PiSugar/PiSugar/model/pisugar_comp.JPG

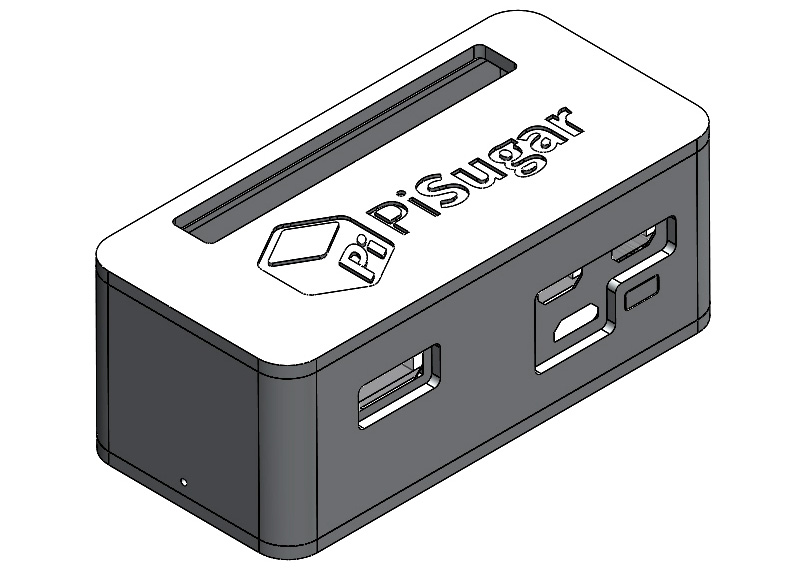
model/pisugar_comp.JPG
