PiSugar/PiSugar/model/pisugar_nobatt_shell.JPG

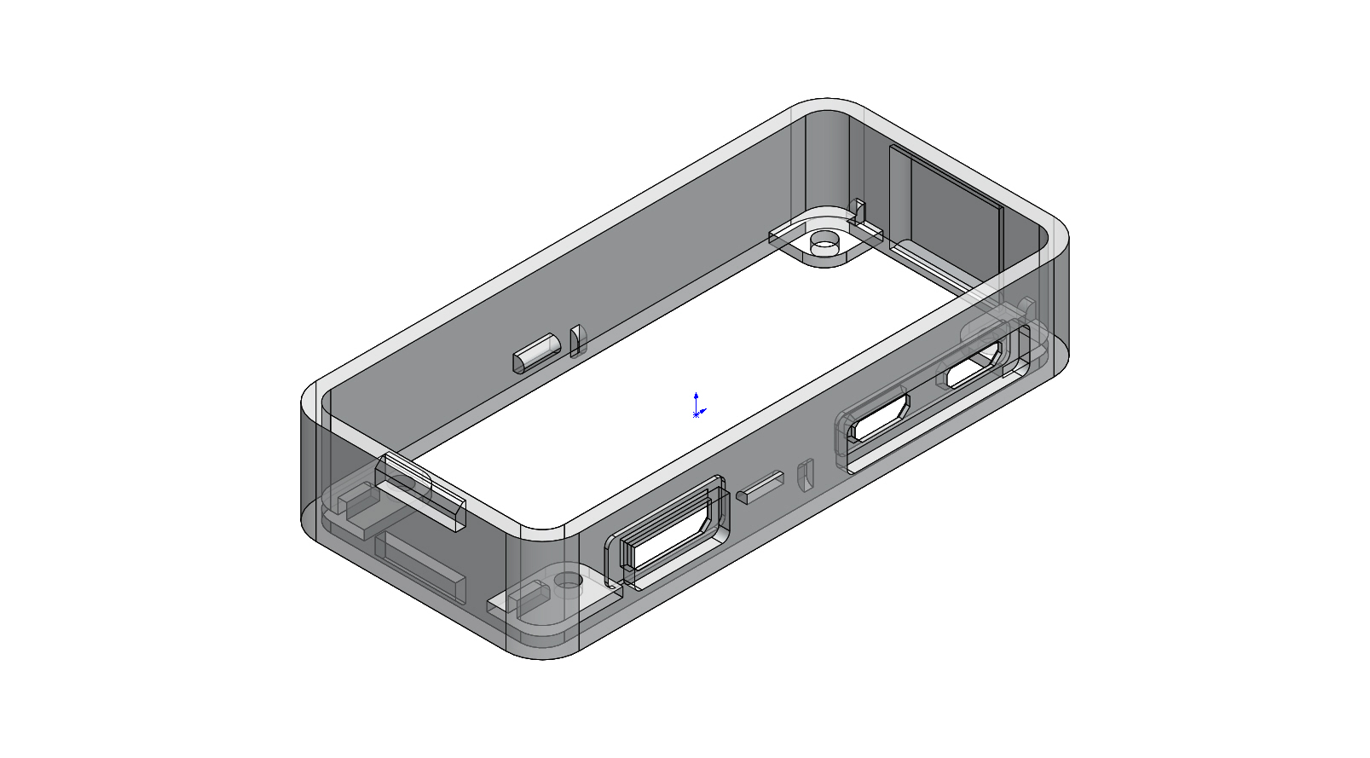
model/pisugar_nobatt_shell.JPG
