PiSugar/PiSugar/model_pro/comp-1.JPG

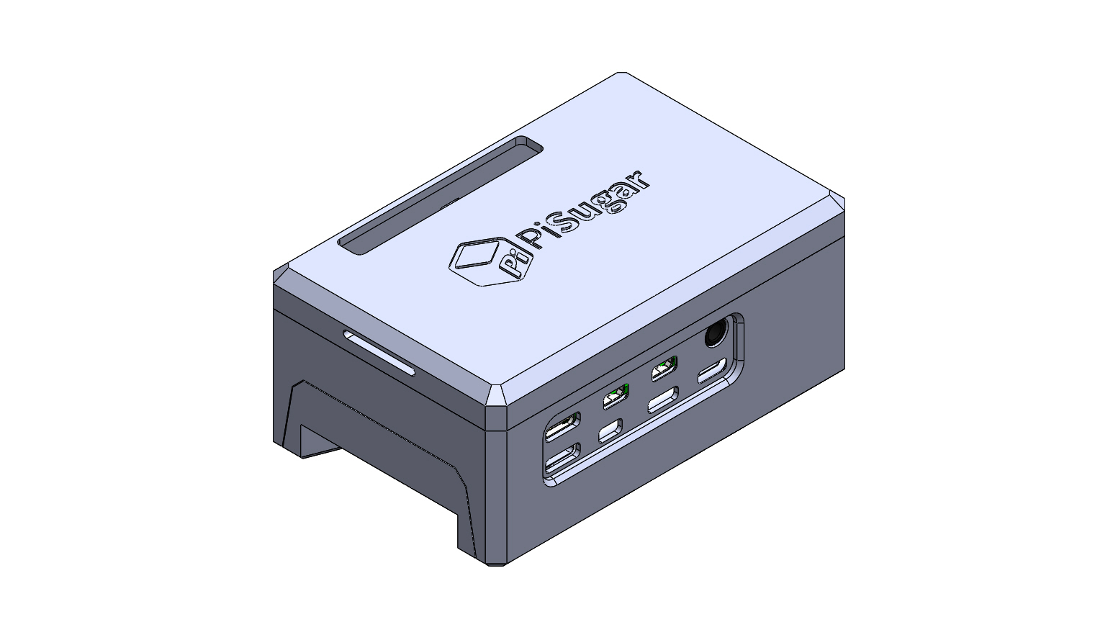
model_pro/comp-1.JPG
