PiSugar/PiSugar/model_pro/comp-2.JPG

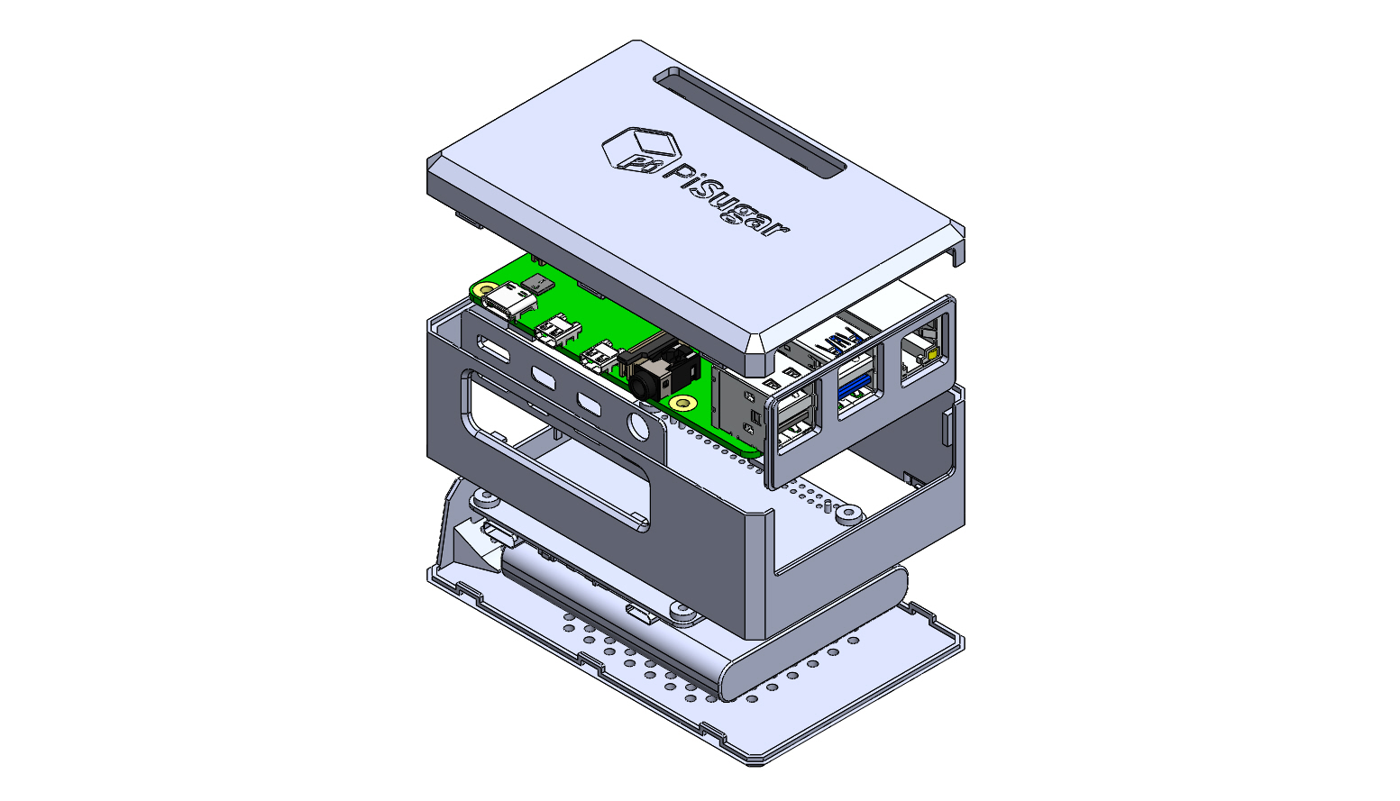
model_pro/comp-2.JPG
