PiSugar/PiSugar/model3/step/pisugar_case_common_cap.STEP

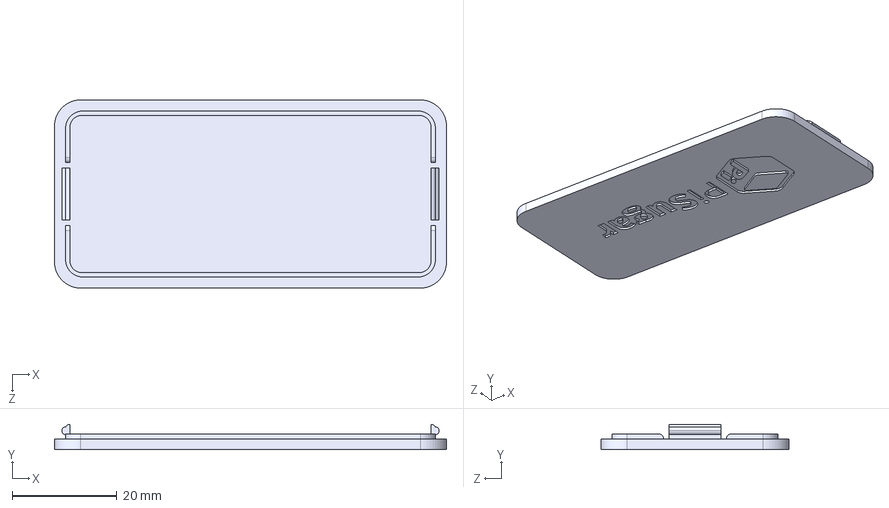
[picture p33: CAD file, 2024-06-06]
model3/step/pisugar_case_common_cap.STEP
75.0 x 4.80 x 36.0 mm
