PiSugar/PiSugar/model_pro/lid/3.52inch-epaper/3.52inch-epaper.SLDPRT

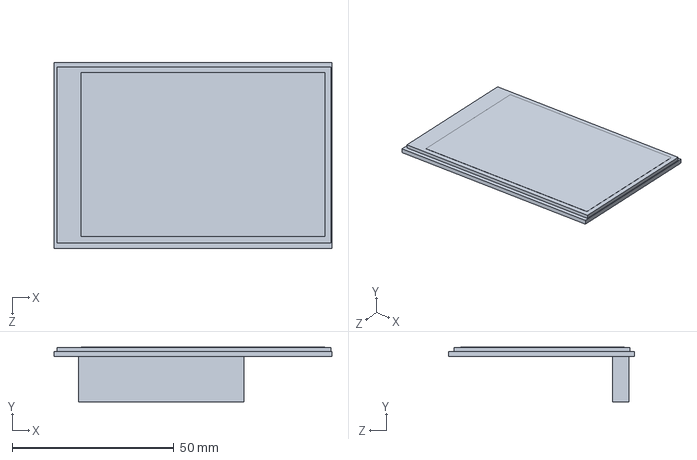
[picture p34: CAD file, 2024-07-05]
model_pro/lid/3.52inch-epaper/3.52inch-epaper.SLDPRT
86.0 x 17.0 x 57.4 mm
