PiSugar/PiSugar/model_pro/pisugar3plus.STEP

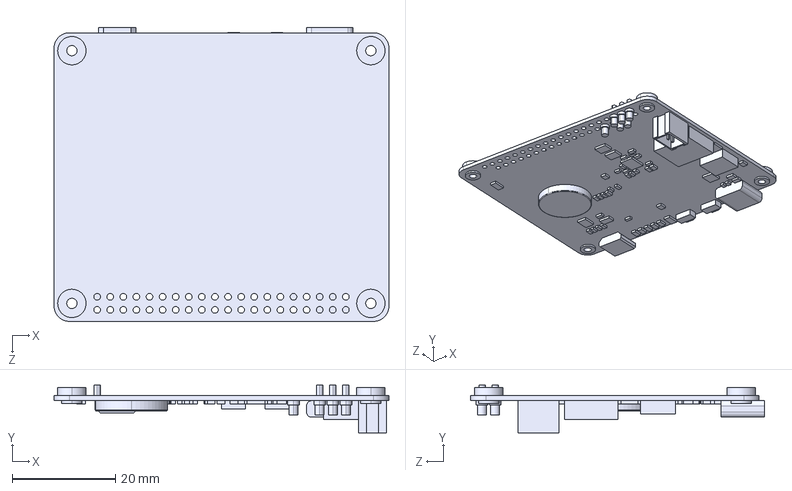
[picture p35: CAD file, 2025-03-03]
model_pro/pisugar3plus.STEP
65.0 x 9.22 x 57.0 mm
