PiSugar/PiSugar/model_pro/step/switch.STEP

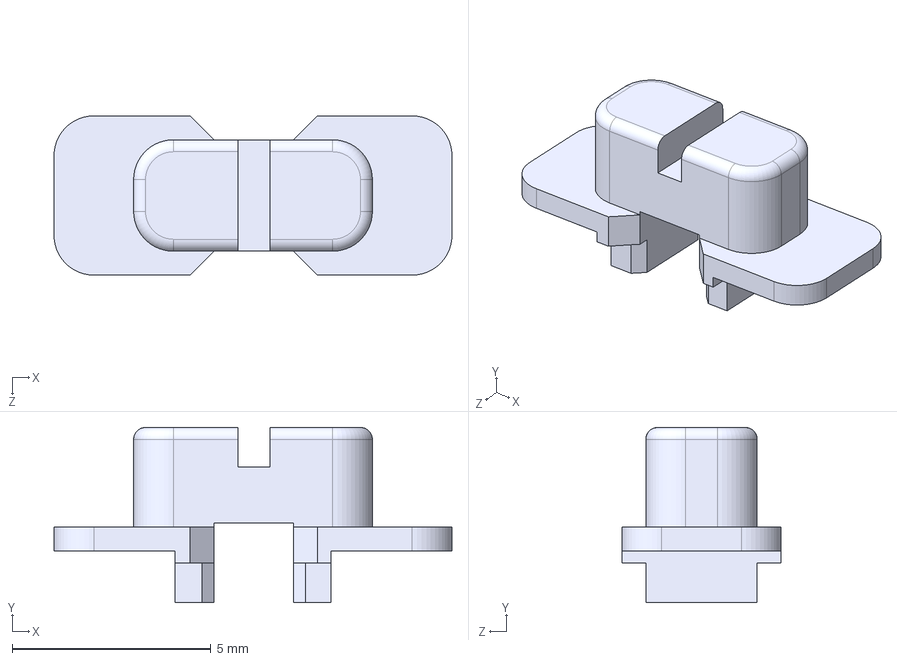
[picture p36: CAD file, 2024-06-06]
model_pro/step/switch.STEP
10.0 x 4.40 x 4.00 mm
