PiSugar/PiSugar/model/pisugar_case_shell_xl.SLDPRT

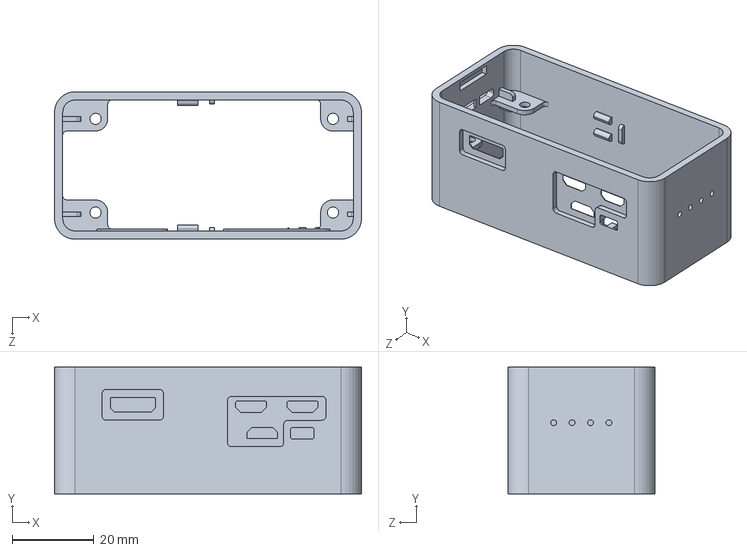
[picture p37: CAD file, 2019-11-30]
model/pisugar_case_shell_xl.SLDPRT
75.0 x 31.0 x 36.0 mm
