PiSugar/PiSugar/model2/pisugar2_button_batch.SLDPRT

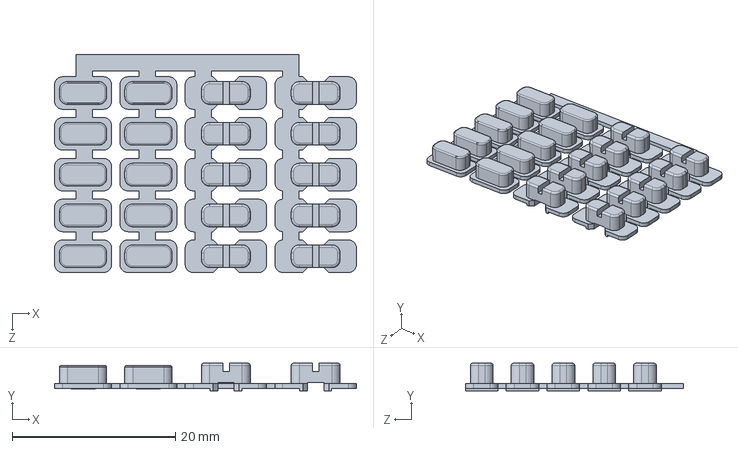
[picture p38: CAD file, 2022-10-15]
model2/pisugar2_button_batch.SLDPRT
37.0 x 3.40 x 26.7 mm
