PiSugar/PiSugar/model3/step/pisugar3_button.STEP

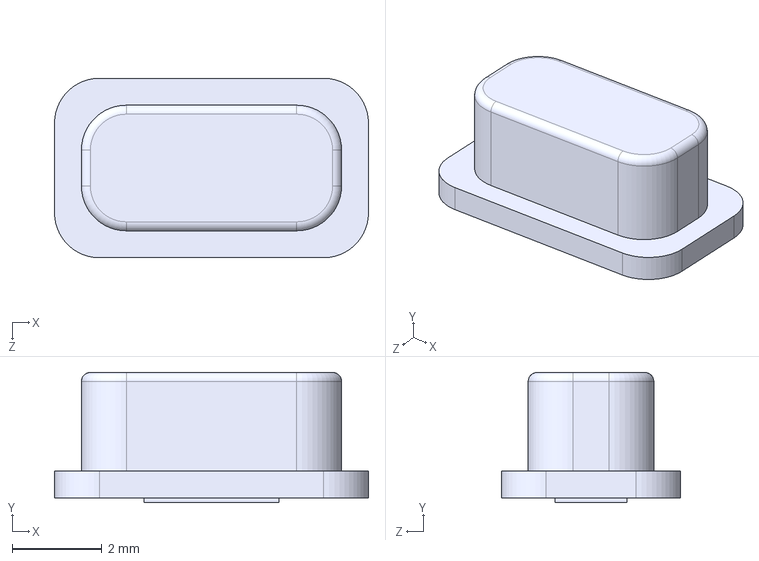
[picture p39: CAD file, 2024-06-06]
model3/step/pisugar3_button.STEP
7.00 x 2.90 x 4.00 mm
