PiSugar/PiSugar/model_pro/step/port-panel-3b-2p.STEP

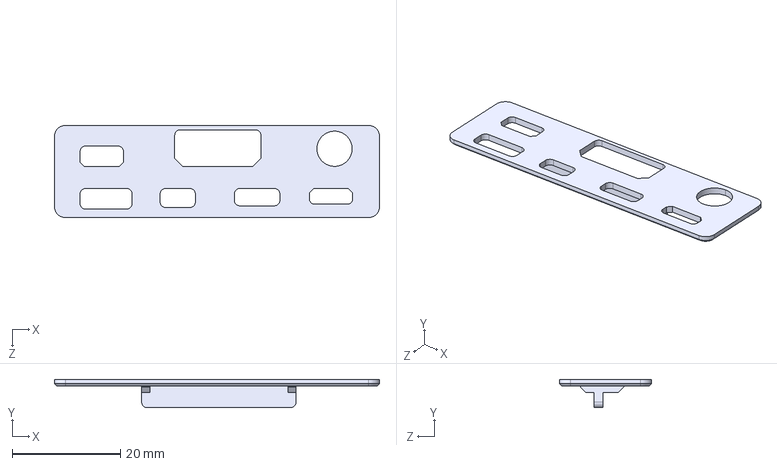
[picture p40: CAD file, 2024-06-06]
model_pro/step/port-panel-3b-2p.STEP
60.0 x 5.20 x 17.0 mm
