PiSugar/PiSugar/model_pro/top.SLDPRT

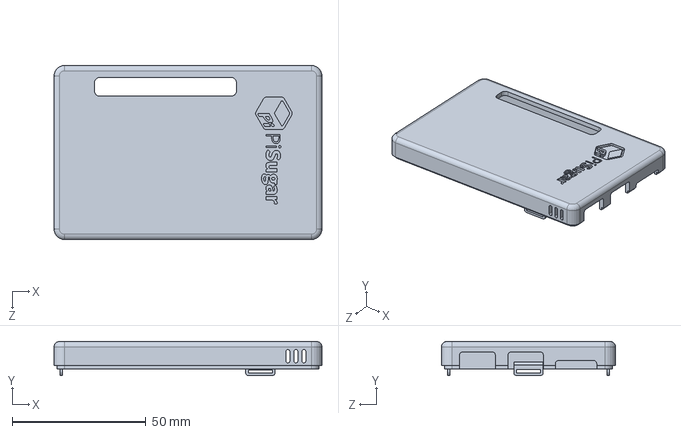
[picture p41: CAD file, 2024-06-06]
model_pro/top.SLDPRT
100.0 x 12.7 x 65.0 mm
