PiSugar/PiSugar/model2/pisugar2_shell_thin.SLDPRT

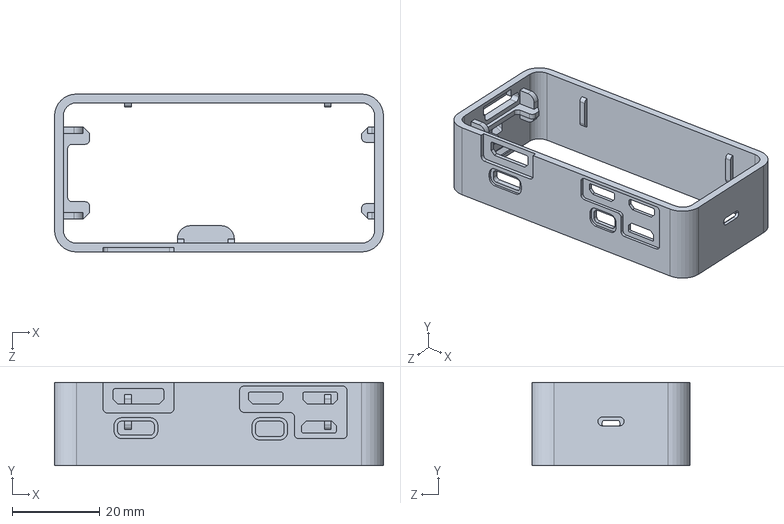
[picture p42: CAD file, 2021-06-01]
model2/pisugar2_shell_thin.SLDPRT
75.0 x 19.0 x 36.0 mm
