PiSugar/PiSugar/model3/step/pisugar3_shell_xl.STEP

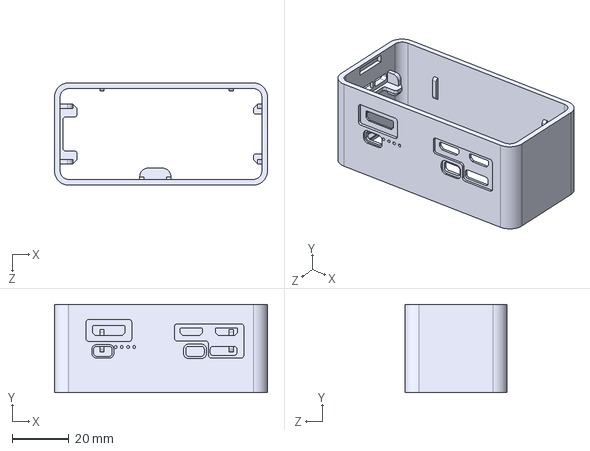
[picture p43: CAD file, 2024-06-06]
model3/step/pisugar3_shell_xl.STEP
75.0 x 31.0 x 36.0 mm
