PiSugar/PiSugar/model_pro/Ras Pi 3B+.SLDPRT

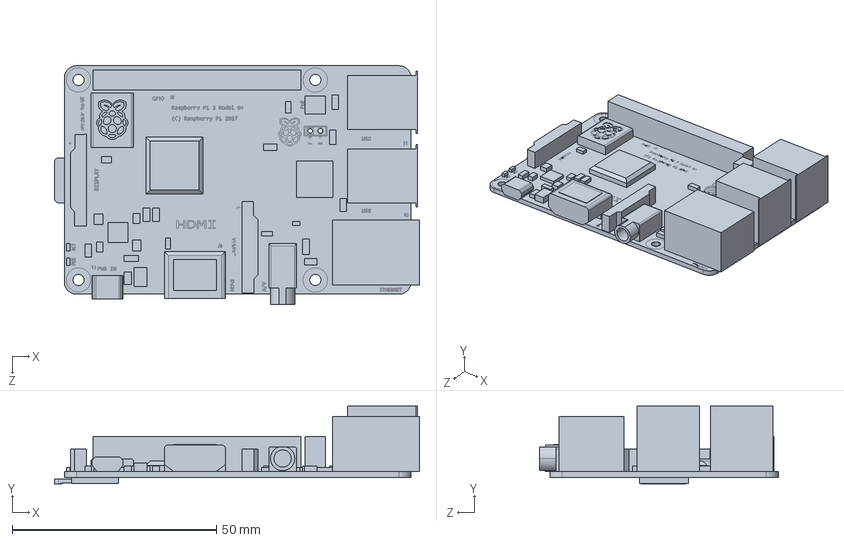
[picture p44: CAD file, 2024-06-06]
model_pro/Ras Pi 3B+.SLDPRT
89.4 x 19.1 x 58.5 mm
