PiSugar/PiSugar/model/pisugar_case_thin_shell.SLDPRT

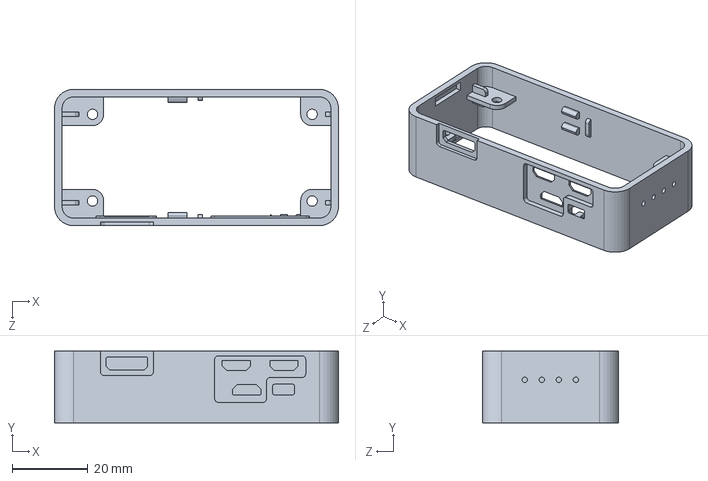
[picture p45: CAD file, 2019-11-04]
model/pisugar_case_thin_shell.SLDPRT
75.0 x 19.0 x 36.0 mm
