PiSugar/PiSugar/model_pro/bottom.SLDPRT

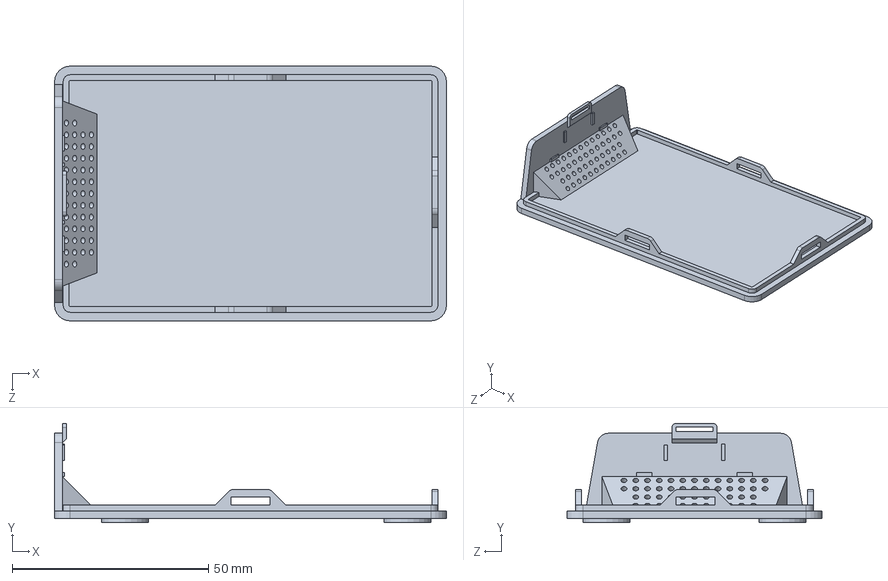
[picture p46: CAD file, 2024-06-06]
model_pro/bottom.SLDPRT
100.0 x 25.3 x 65.0 mm
