PiSugar/PiSugar/model_pro/step/pro_shell.STEP

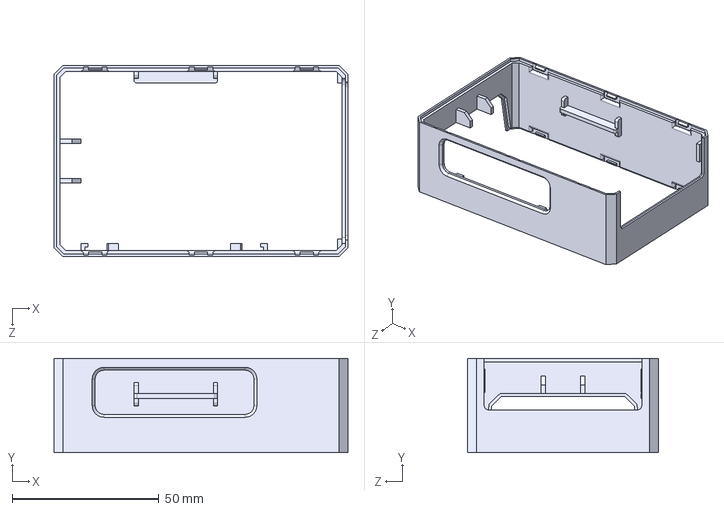
[picture p47: CAD file, 2024-06-06]
model_pro/step/pro_shell.STEP
100.0 x 32.0 x 65.0 mm
