PiSugar/PiSugar/model/pisugar_thin_nobatt_shell.SLDPRT

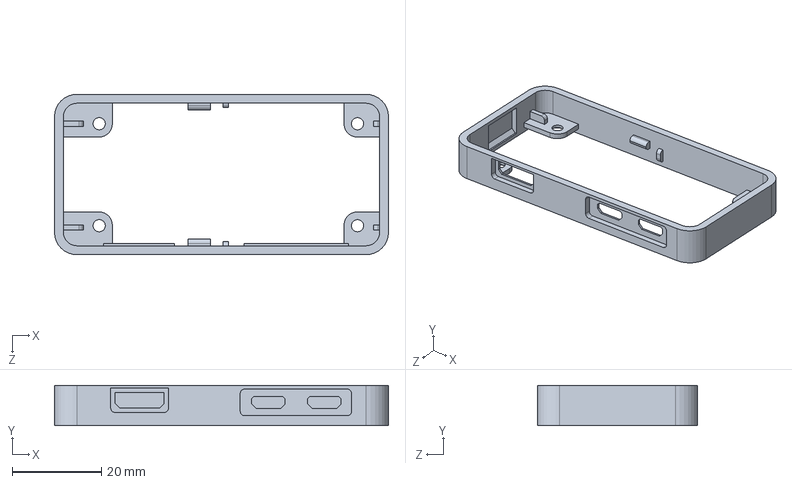
[picture p48: CAD file, 2019-06-25]
model/pisugar_thin_nobatt_shell.SLDPRT
75.0 x 9.00 x 36.0 mm
