PiSugar/PiSugar/model_pro/fan.SLDPRT

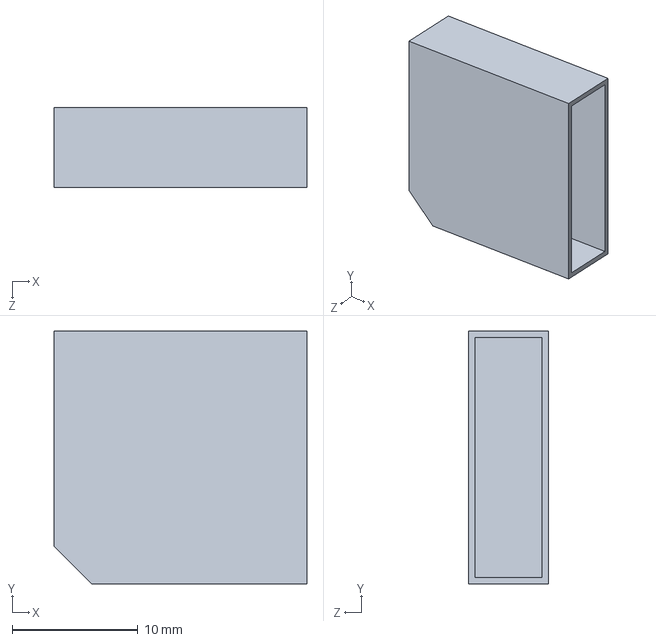
[picture p49: CAD file, 2024-06-06]
model_pro/fan.SLDPRT
20.2 x 20.2 x 6.36 mm
