PiSugar/PiSugar/model/pisugar_nobatt_shell.SLDPRT

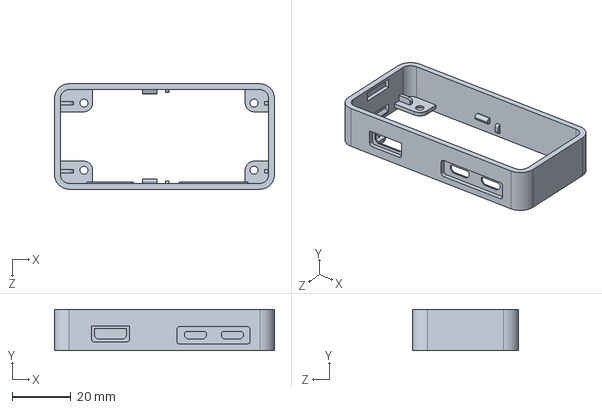
[picture p51: CAD file, 2019-06-25]
model/pisugar_nobatt_shell.SLDPRT
75.0 x 14.0 x 36.0 mm
