PiSugar/PiSugar/model2/pisugar2_switch.SLDPRT

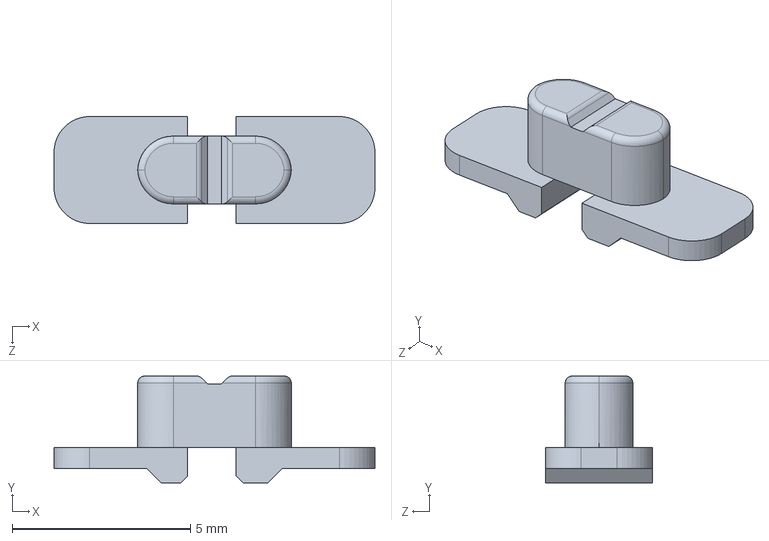
[picture p52: CAD file, 2020-06-27]
model2/pisugar2_switch.SLDPRT
9.00 x 3.00 x 3.00 mm
