PiSugar/PiSugar/model_pro/batt5000.SLDPRT

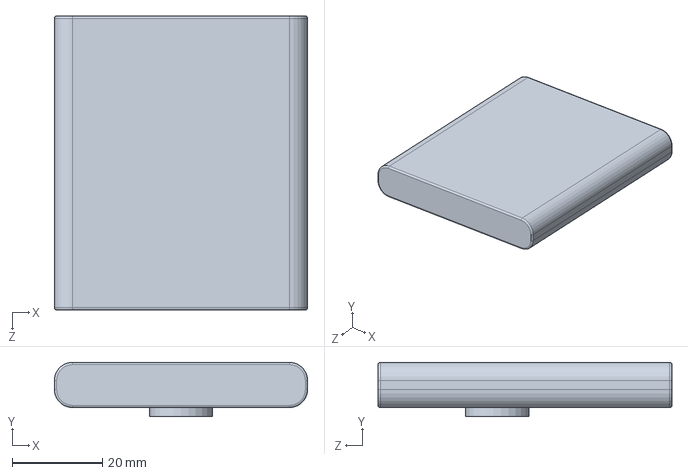
[picture p53: CAD file, 2024-06-06]
model_pro/batt5000.SLDPRT
56.0 x 12.0 x 65.0 mm
