PiSugar/PiSugar/model/pisugar_holder.SLDPRT

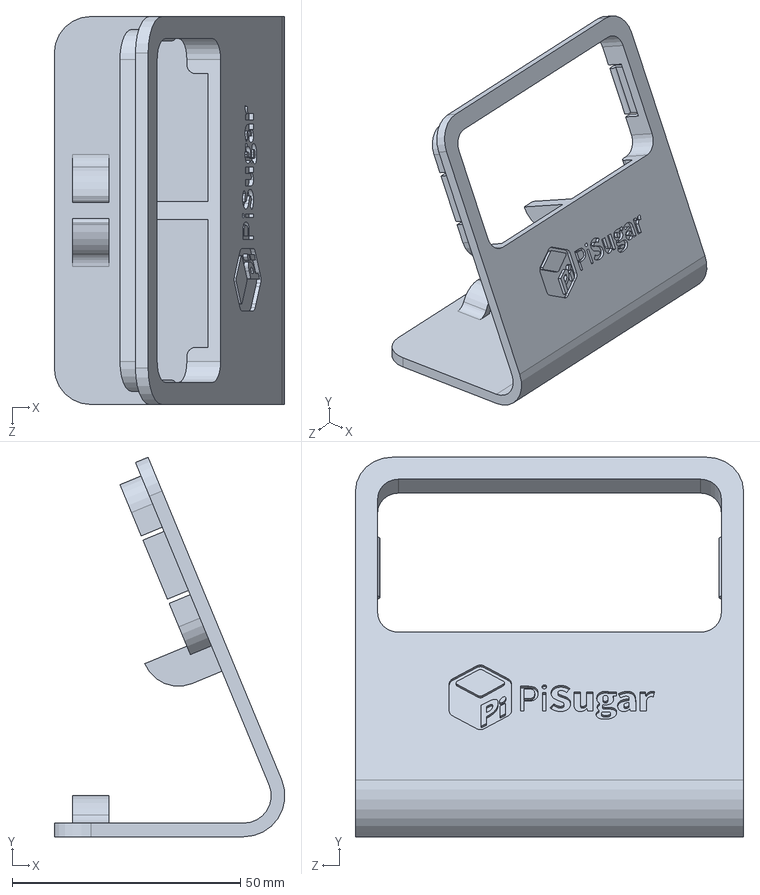
[picture p54: CAD file, 2019-05-16]
model/pisugar_holder.SLDPRT
50.5 x 83.1 x 85.0 mm
