PiSugar/PiSugar/model2/pisugar2_shell_xl - pisugar2_switch-1.STL

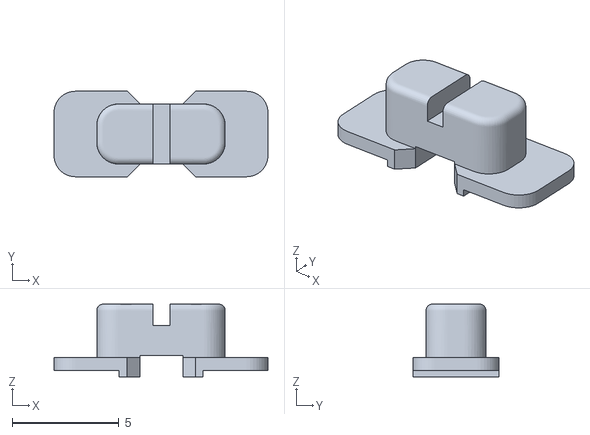
[picture p55: CAD file, 2020-06-27]
model2/pisugar2_shell_xl - pisugar2_switch-1.STL
10.0 x 4.00 x 3.40
