PiSugar/PiSugar/model/glass.SLDPRT

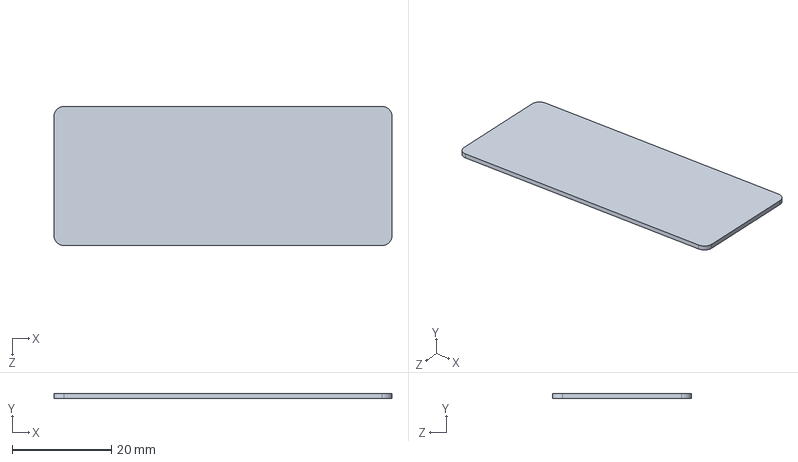
[picture p56: CAD file, 2019-04-10]
model/glass.SLDPRT
68.0 x 1.00 x 28.0 mm
