PiSugar/PiSugar/model/pisugar_case_button_comp.SLDPRT

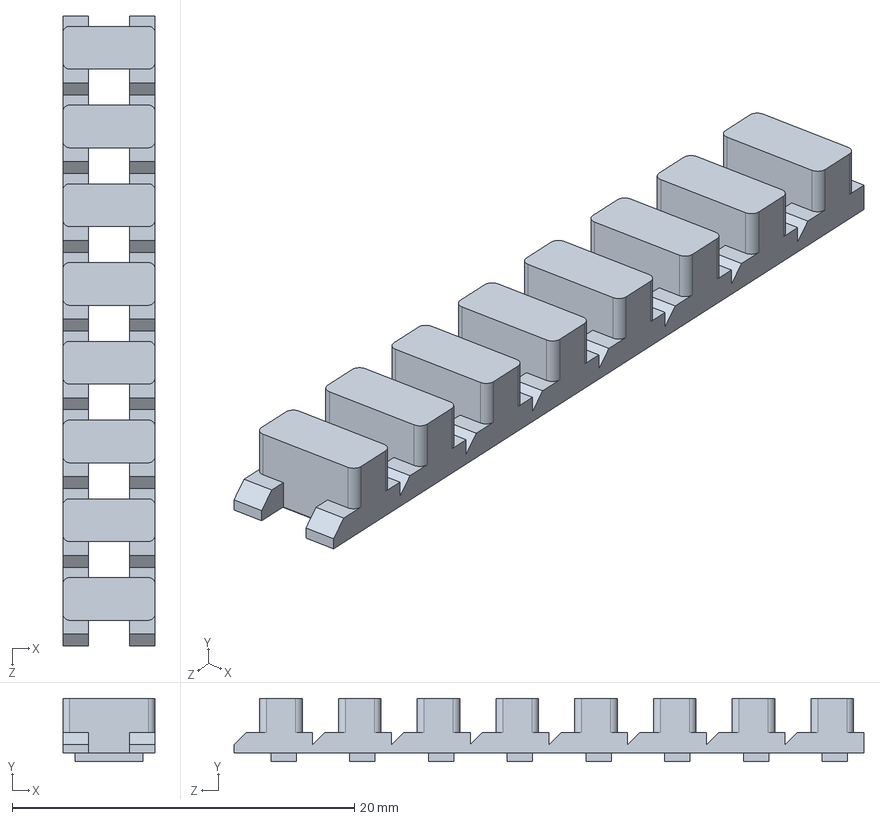
[picture p57: CAD file, 2019-04-10]
model/pisugar_case_button_comp.SLDPRT
5.40 x 3.70 x 36.8 mm
