PiSugar/PiSugar/model/pisugar_case_button.SLDPRT

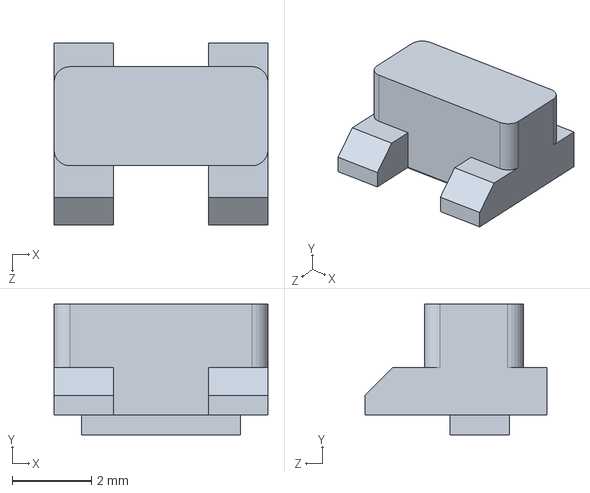
[picture p58: CAD file, 2019-04-10]
model/pisugar_case_button.SLDPRT
5.40 x 3.30 x 4.60 mm
