PiSugar/PiSugar/model_pro/pro - usb-panel-3b-1.STL

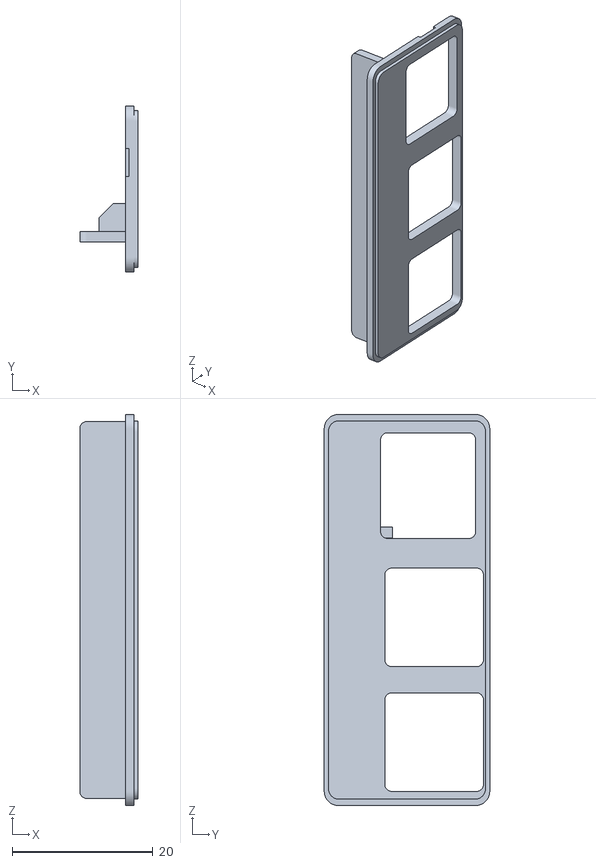
[picture p59: CAD file, 2022-04-29]
model_pro/pro - usb-panel-3b-1.STL
8.30 x 23.5 x 55.5
