PiSugar/PiSugar/model/pisugar_case_top_cap.SLDPRT

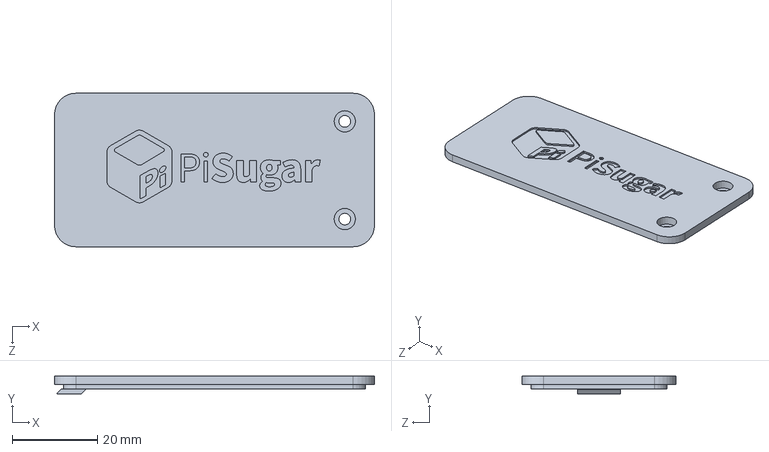
[picture p60: CAD file, 2019-03-25]
model/pisugar_case_top_cap.SLDPRT
75.0 x 4.20 x 36.0 mm
