PiSugar/PiSugar/model/pisugar_case_all.SLDPRT

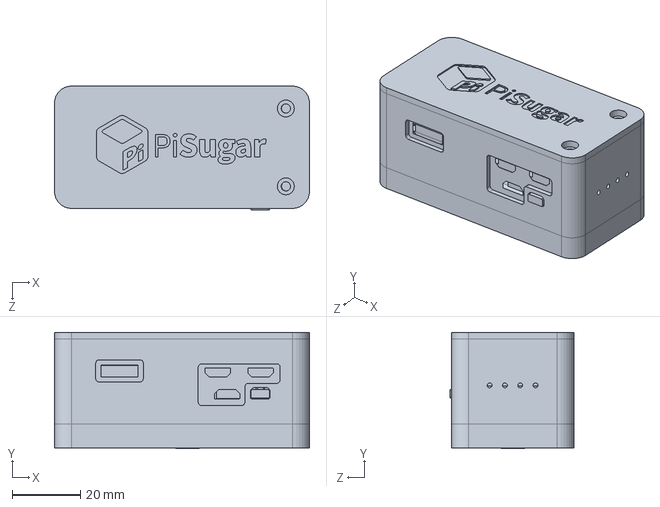
[picture p61: CAD file, 2019-03-12]
model/pisugar_case_all.SLDPRT
75.0 x 34.2 x 36.4 mm
