PiSugar/PiSugar/model/pizero.SLDPRT

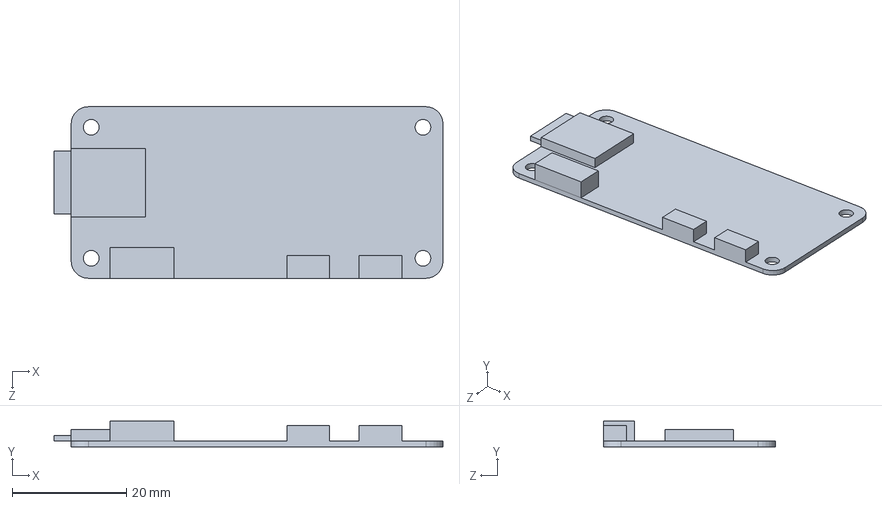
[picture p62: CAD file, 2019-03-04]
model/pizero.SLDPRT
68.0 x 4.50 x 30.0 mm
