PiSugar/PiSugar/model/standoffs.SLDPRT

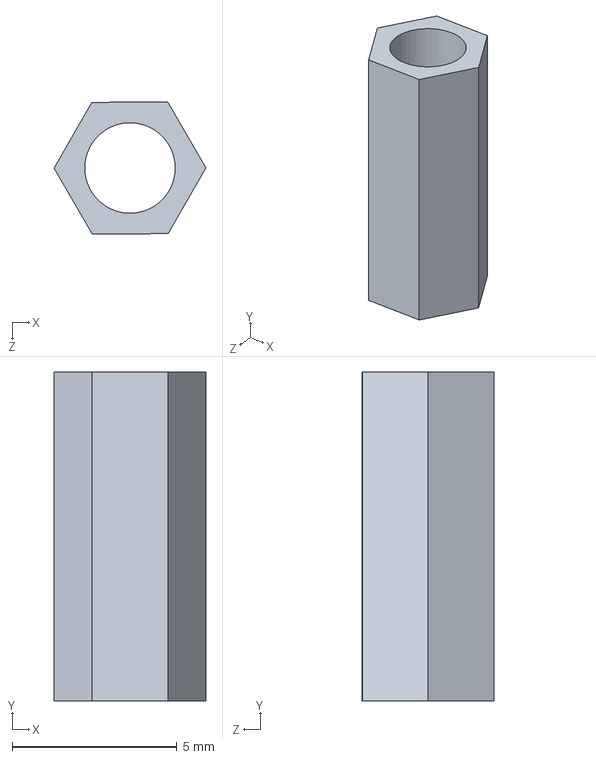
[picture p63: CAD file, 2018-12-23]
model/standoffs.SLDPRT
4.62 x 10.0 x 4.01 mm
