PiSugar/PiSugar/model_pro/side-panel.SLDPRT

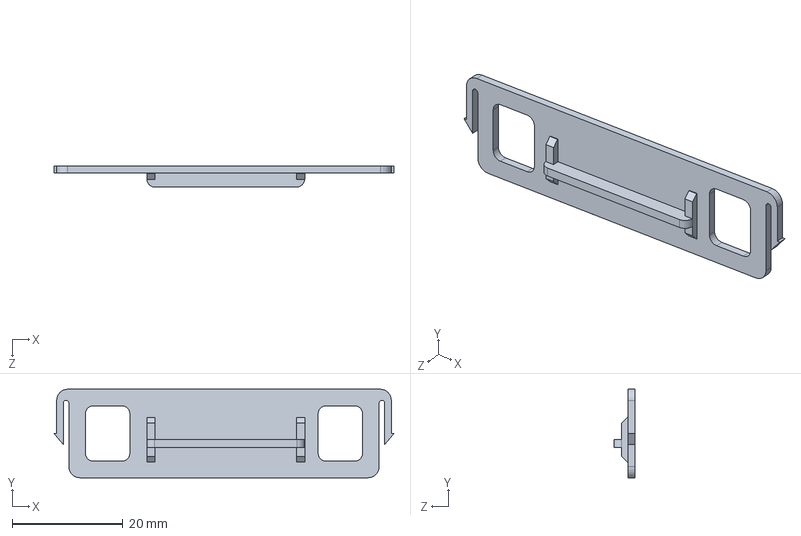
[picture p64: CAD file, 2021-03-12]
model_pro/side-panel.SLDPRT
61.4 x 16.0 x 3.80 mm
