PiSugar/PiSugar/model/battery900.SLDPRT

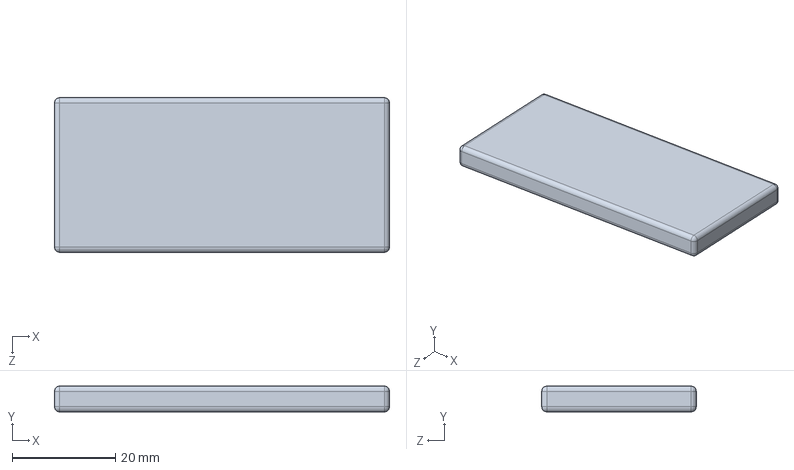
[picture p65: CAD file, 2018-12-23]
model/battery900.SLDPRT
65.0 x 5.00 x 30.0 mm
