PiSugar/PiSugar/model_pro/pro - bottom.STL

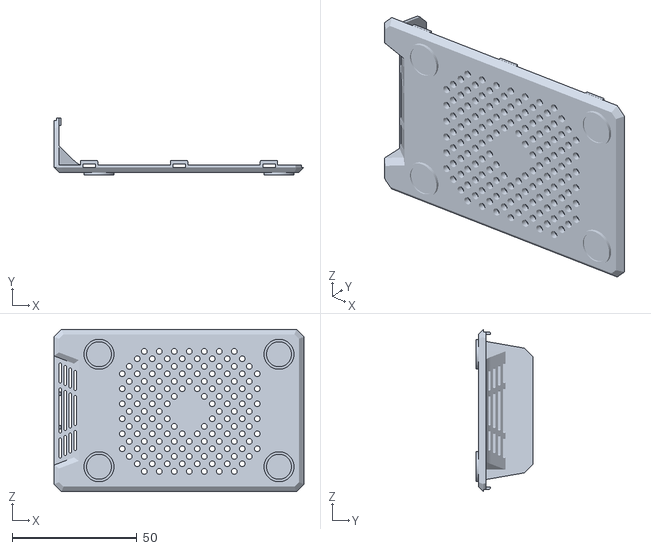
[picture p66: CAD file, 2021-03-12]
model_pro/pro - bottom.STL
100.0 x 22.8 x 65.0
