PiSugar/PiSugar/model/pisugar.SLDPRT

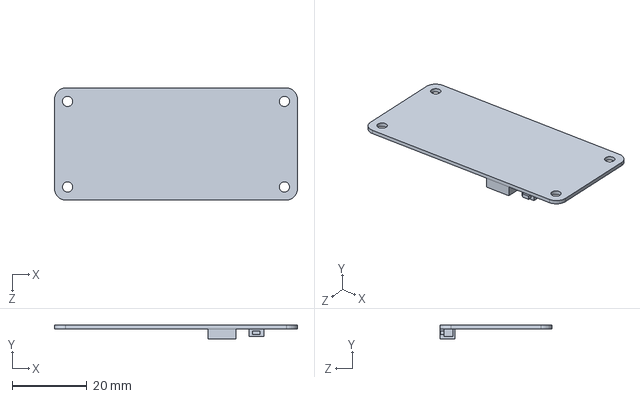
[picture p67: CAD file, 2018-12-23]
model/pisugar.SLDPRT
65.0 x 3.70 x 30.0 mm
