PiSugar/PiSugar/model_pro/pro - top.STL

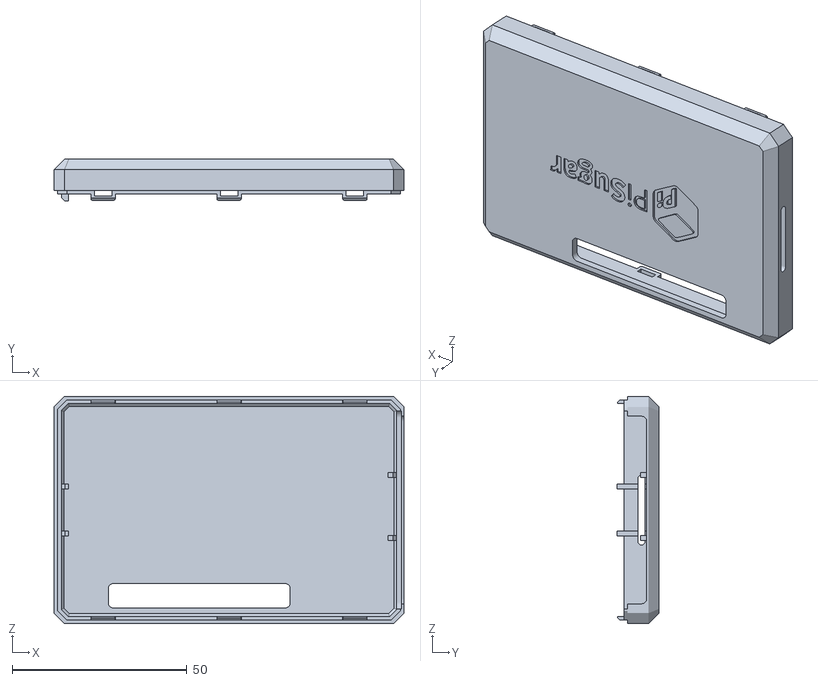
[picture p68: CAD file, 2021-03-12]
model_pro/pro - top.STL
100.0 x 12.0 x 65.0
