PiSugar/PiSugar/model_pro/pro - bottom-18650.STL

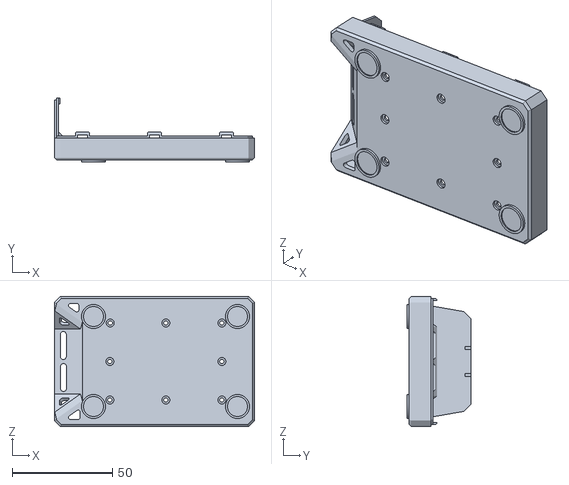
[picture p69: CAD file, 2021-03-12]
model_pro/pro - bottom-18650.STL
100.0 x 31.8 x 65.0
